t3chN0Mad/OpenXPBMS/PCB/PCB.sch

## KiCad design PCB/PCB.sch (2020-01-07)

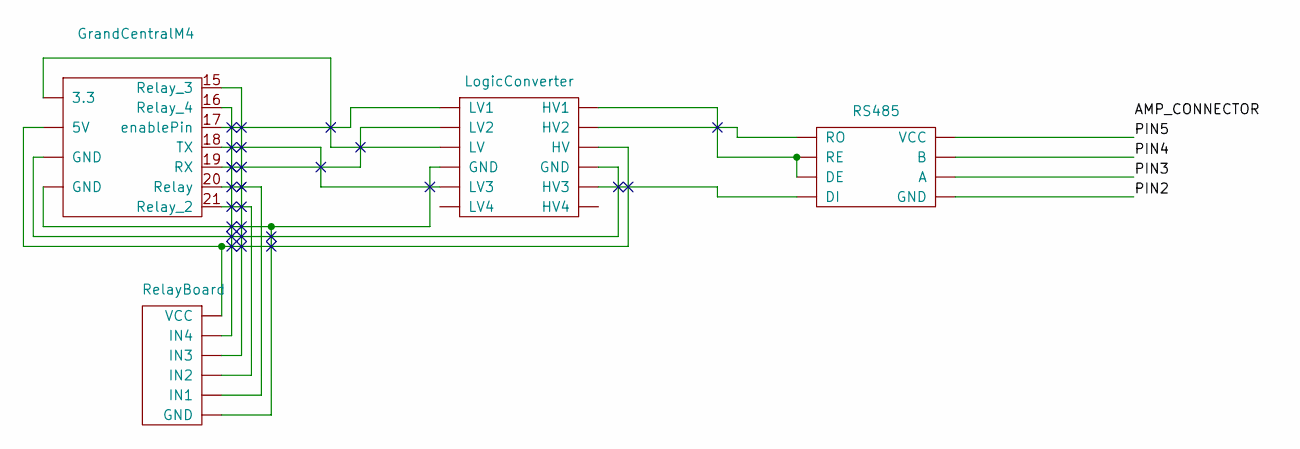
[picture p2: schematic PCB.sch]

Parts:
U1: GrandCentralM4
U2: RelayBoard
U3: LogicConverter
U4: RS485

Connections:
unnamed: U1.15 (Relay_3), U2.~
unnamed: U1.16 (Relay_4), U2.~
unnamed: U1.17 (enablePin), U3.~
unnamed: U1.18 (TX), U3.~
unnamed: U1.19 (RX), U3.~
unnamed: U1.20 (Relay), U2.~
unnamed: U1.21 (Relay_2), U2.~
unnamed: U1.~ (3.3), U2.~, U3.~
unnamed: U3.~, U4.~
PIN2: U4.~
PIN3: U4.~
PIN4: U4.~
PIN5: U4.~
